Robotmad/EMFBadge-Hexpansions-GPS/Images/hexpansion-L80-3.jpg

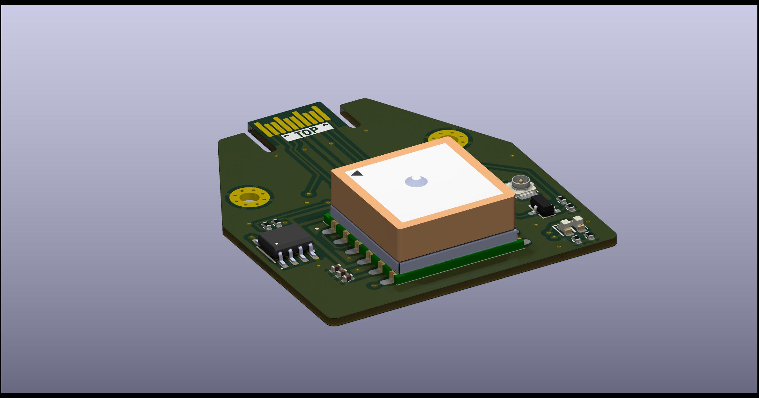
Images/hexpansion-L80-3.jpg
