Robotmad/EMFBadge-Hexpansions-GPS/Images/hexpansion-L80-8.jpg

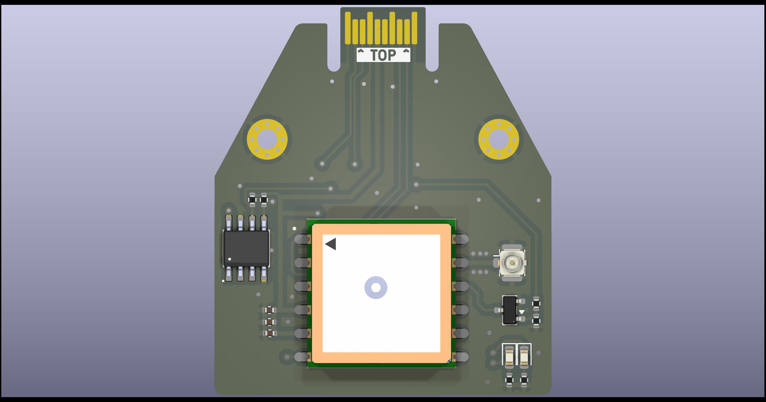
Images/hexpansion-L80-8.jpg
